Emute-Lab-Instruments/uSEQ/hardware/version0.2/panel/uSEQ-panel_outlined.pdf

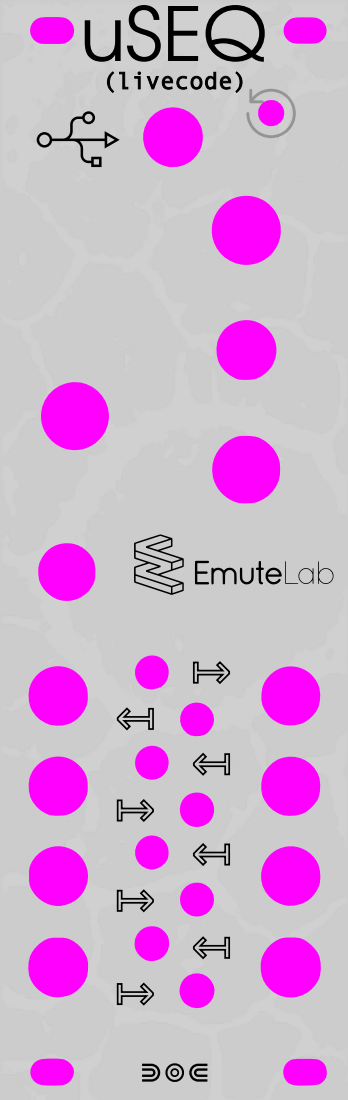
[picture p3: page 1]
