Emute-Lab-Instruments/uSEQ/uSEQ/src/signal_engine/signal_engine.h

#ifndef SIGNAL_ENGINE_H
#define SIGNAL_ENGINE_H

// Convenience header: includes all signal engine components.

#include "types.h"
#include "diagnostics.h"
#include "token.h"
#include "cell_store.h"
#include "node_pool.h"
#include "graph_builder.h"
#include "executor.h"
#include "cold_eval.h"

#endif // SIGNAL_ENGINE_H
