Emute-Lab-Instruments/uSEQ/hardware/version0.2/img/cable-trimmed.jpg

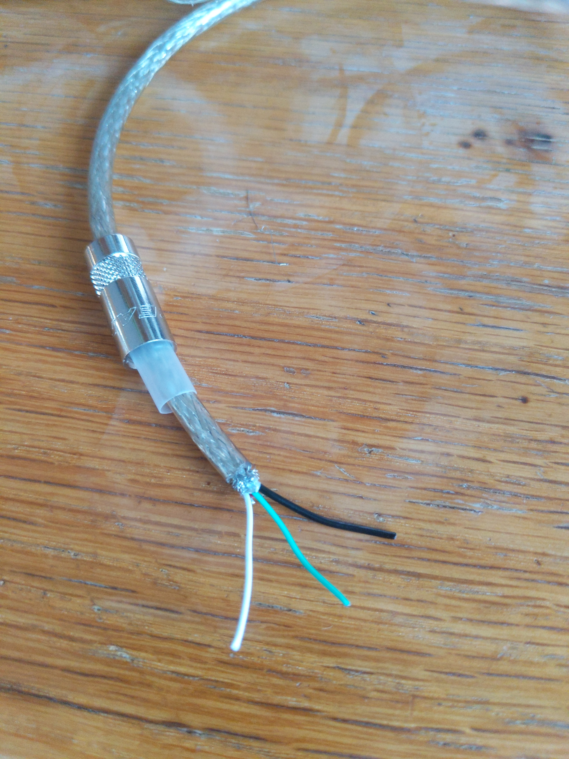
[picture p16: hardware/version0.2/img/cable-trimmed.jpg]
hardware/version0.2/img/cable-trimmed.jpg
